afandihrp/Sistem-Monitoring-Lahan-berbasis-ESP32CAM-relatif-murah/zfoto/4.png

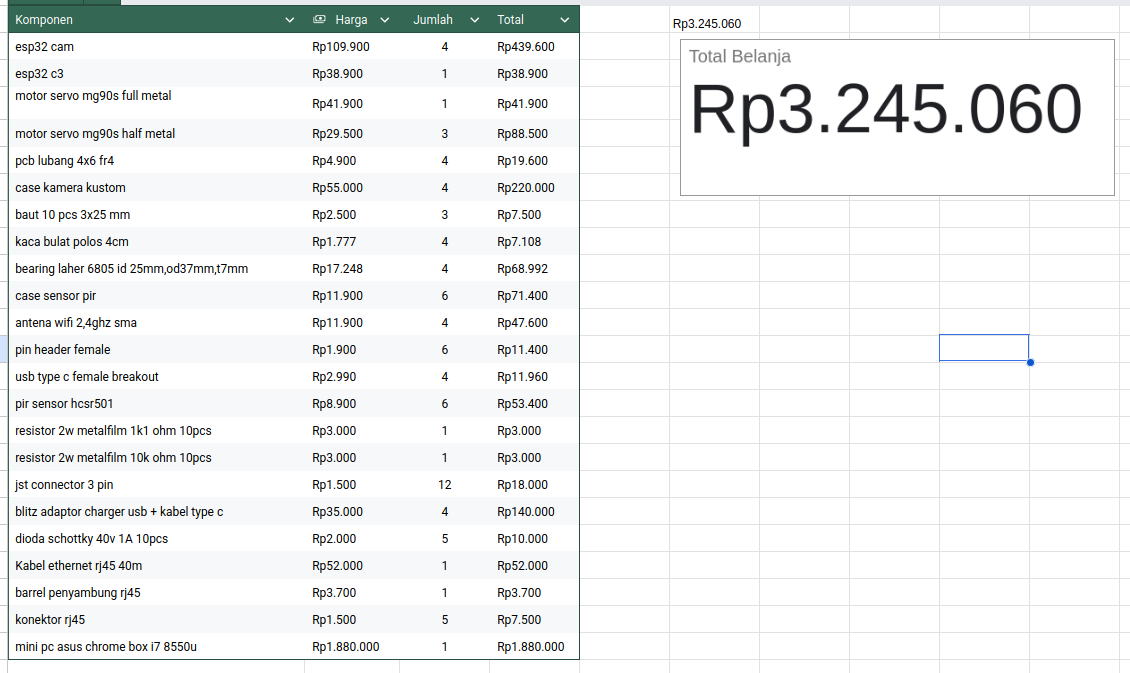
zfoto/4.png
