afandihrp/Sistem-Monitoring-Lahan-berbasis-ESP32CAM-relatif-murah/zfoto/tampak masuk notifikasi telegram .png

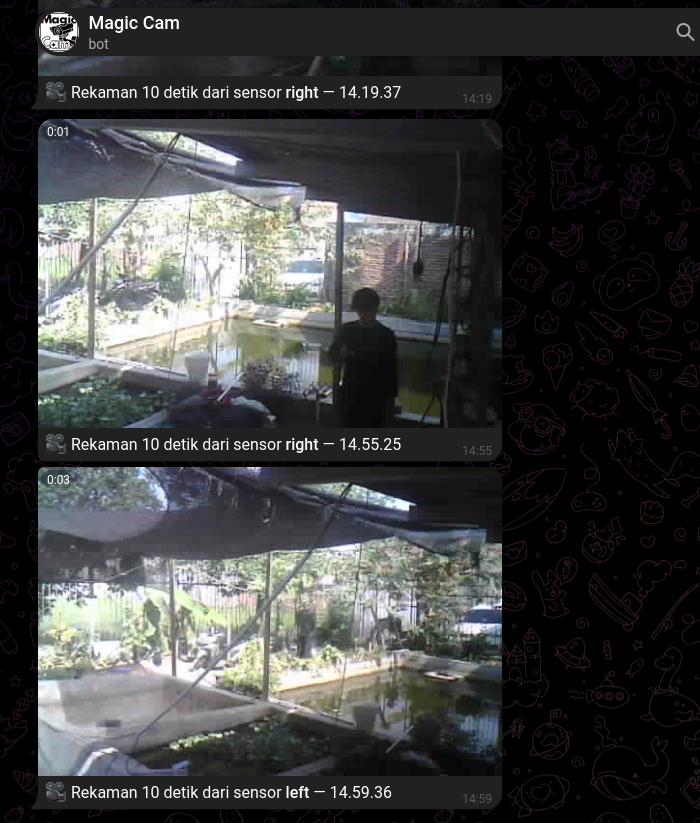
zfoto/tampak masuk notifikasi telegram .png
